JaneliaSciComp/power_switch_controller/firmware/PowerSwitchController.cpp

// ----------------------------------------------------------------------------
// PowerSwitchController.cpp
//
// Authors:
// Peter Polidoro polidorop@janelia.hhmi.org
// ----------------------------------------------------------------------------
#include "PowerSwitchController.h"

PowerSwitchController::PowerSwitchController() :
  PowerSwitch(constants::cs_pin,constants::in_pin)
{
}

void PowerSwitchController::init()
{
  PowerSwitch::init(constants::ic_count);
  pinMode(constants::led_pwr_pin,INPUT);

  // Device Info
  modular_device.setName(constants::device_name);
  modular_device.setModelNumber(constants::model_number);
  modular_device.setFirmwareNumber(constants::firmware_number);

  // Saved Variables

  // Parameters
  ModularDevice::Parameter& channels_parameter = modular_device.createParameter(constants::channels_parameter_name);
  channels_parameter.setRange(constants::channels_min,constants::channels_max);
  ModularDevice::Parameter& channel_parameter = modular_device.createParameter(constants::channel_parameter_name);
  channel_parameter.setRange(constants::channel_min,constants::channel_max);

  // Methods
  ModularDevice::Method& get_leds_powered_method = modular_device.createMethod(constants::get_leds_powered_method_name);
  get_leds_powered_method.attachCallback(callbacks::getLedsPoweredCallback);

  ModularDevice::Method& set_channels_method = modular_device.createMethod(constants::set_channels_method_name);
  set_channels_method.attachCallback(callbacks::setChannelsCallback);
  set_channels_method.addParameter(channels_parameter);

  ModularDevice::Method& set_channel_on_method = modular_device.createMethod(constants::set_channel_on_method_name);
  set_channel_on_method.attachCallback(callbacks::setChannelOnCallback);
  set_channel_on_method.addParameter(channel_parameter);

  ModularDevice::Method& set_channel_off_method = modular_device.createMethod(constants::set_channel_off_method_name);
  set_channel_off_method.attachCallback(callbacks::setChannelOffCallback);
  set_channel_off_method.addParameter(channel_parameter);

  ModularDevice::Method& set_all_channels_on_method = modular_device.createMethod(constants::set_all_channels_on_method_name);
  set_all_channels_on_method.attachCallback(callbacks::setAllChannelsOnCallback);

  ModularDevice::Method& set_all_channels_off_method = modular_device.createMethod(constants::set_all_channels_off_method_name);
  set_all_channels_off_method.attachCallback(callbacks::setAllChannelsOffCallback);

  ModularDevice::Method& get_channels_on_method = modular_device.createMethod(constants::get_channels_on_method_name);
  get_channels_on_method.attachCallback(callbacks::getChannelsOnCallback);

  ModularDevice::Method& get_channel_count_method = modular_device.createMethod(constants::get_channel_count_method_name);
  get_channel_count_method.attachCallback(callbacks::getChannelCountCallback);
}

void PowerSwitchController::update()
{
}

bool PowerSwitchController::getLedsPowered()
{
  return digitalRead(constants::led_pwr_pin) == HIGH;
}

PowerSwitchController power_switch_controller;
